devsecfranklin/badge-2018-nolacon/artwork/nola_diecut.bmp

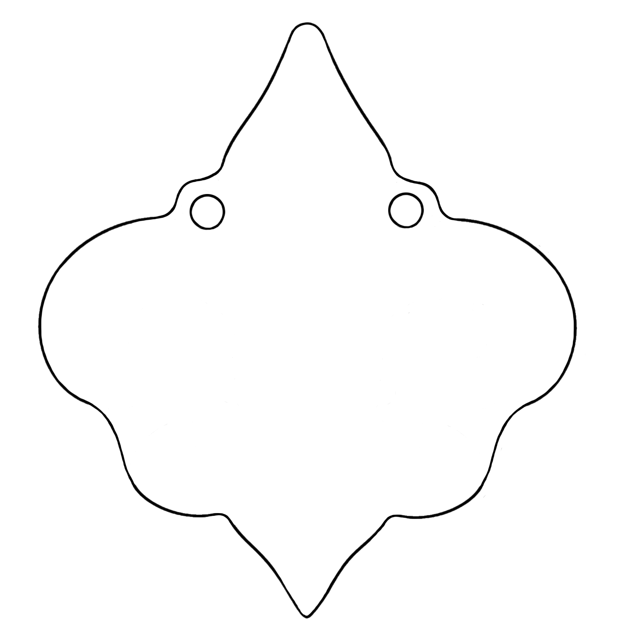
artwork/nola_diecut.bmp
