devsecfranklin/badge-2018-nolacon/artwork/nola_layered_NEW.bmp

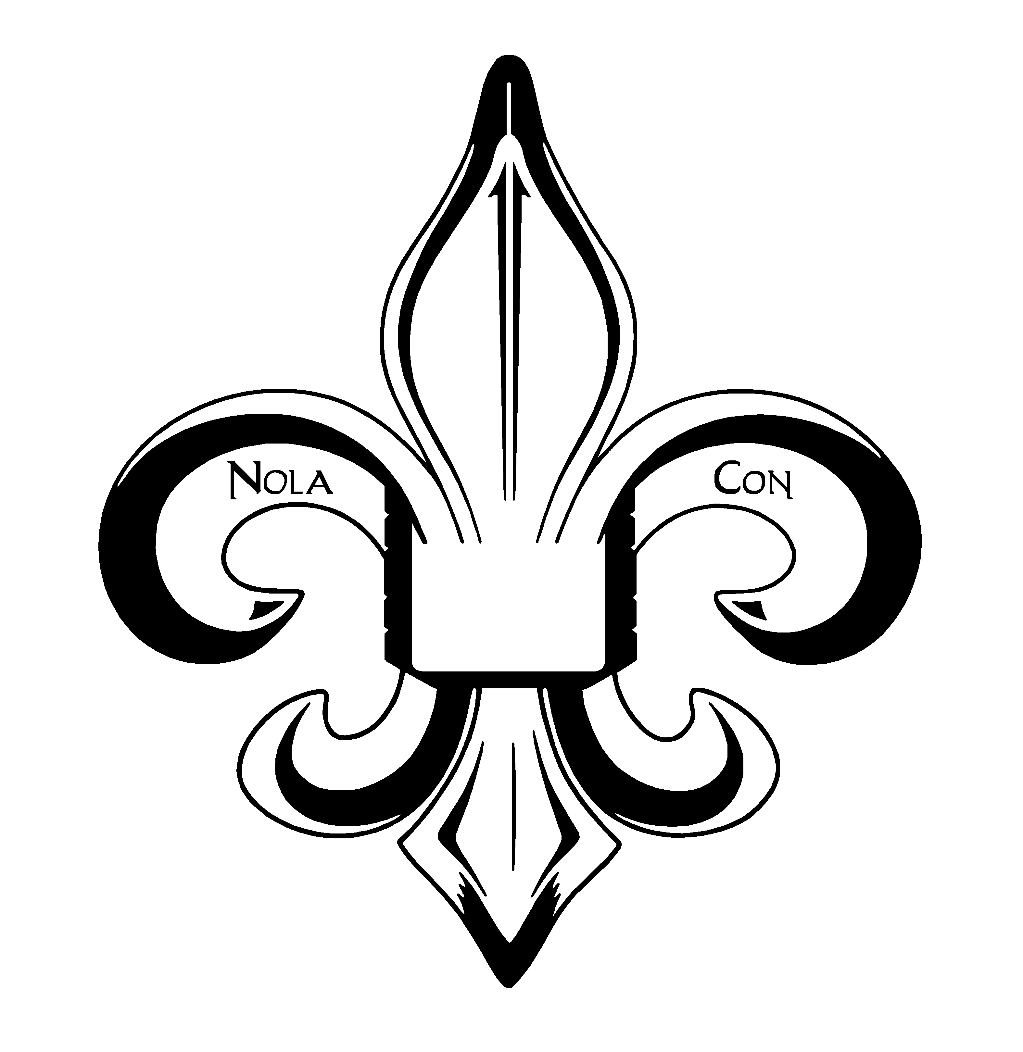
artwork/nola_layered_NEW.bmp
