devsecfranklin/badge-2018-nolacon/images/image1.png

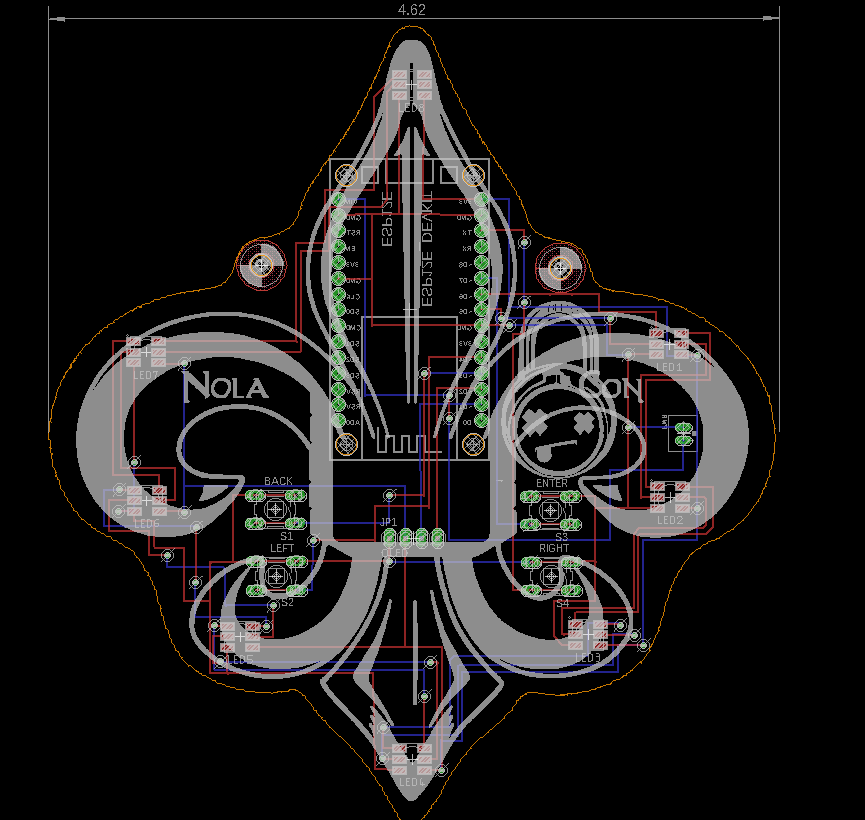
images/image1.png
