devsecfranklin/badge-2018-nolacon/images/image2.jpeg

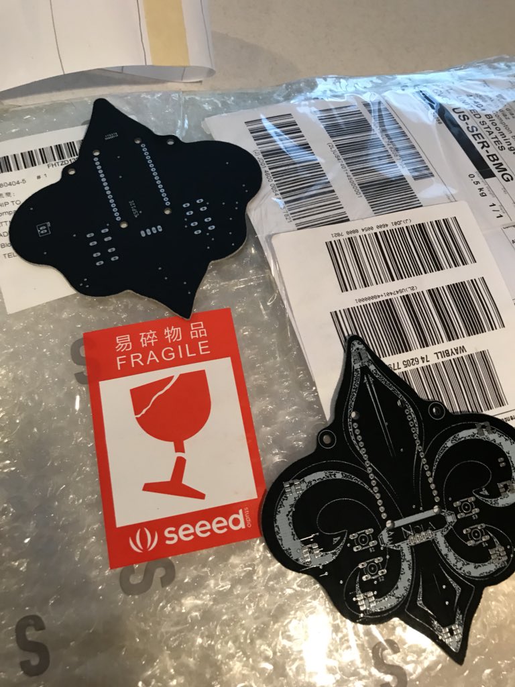
images/image2.jpeg
