devsecfranklin/badge-2018-nolacon/images/image3.jpg

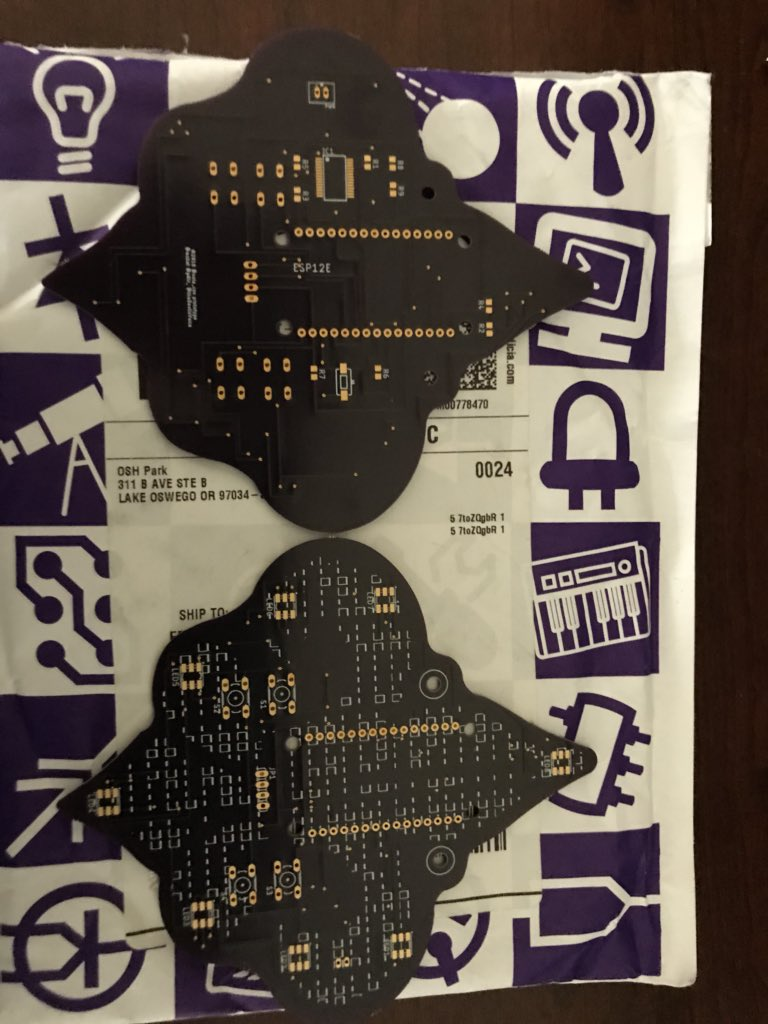
images/image3.jpg
