devsecfranklin/badge-2018-nolacon/images/image4.jpg

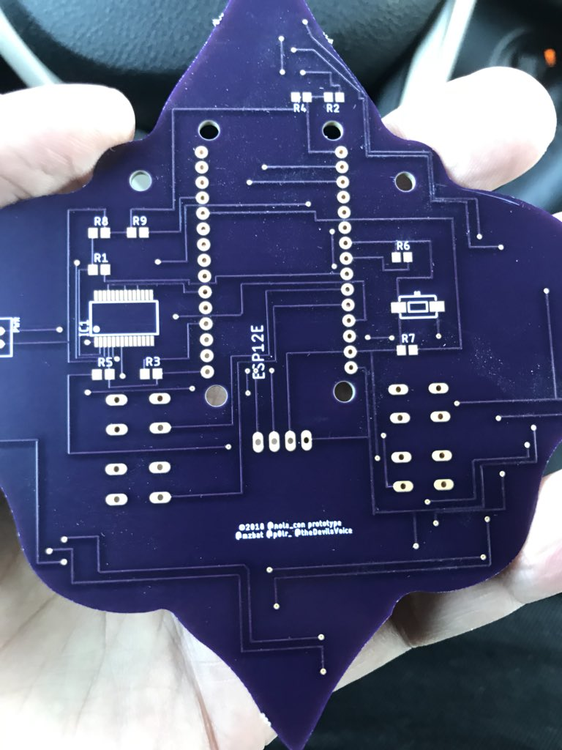
images/image4.jpg
