devsecfranklin/badge-2018-nolacon/images/image6.jpg

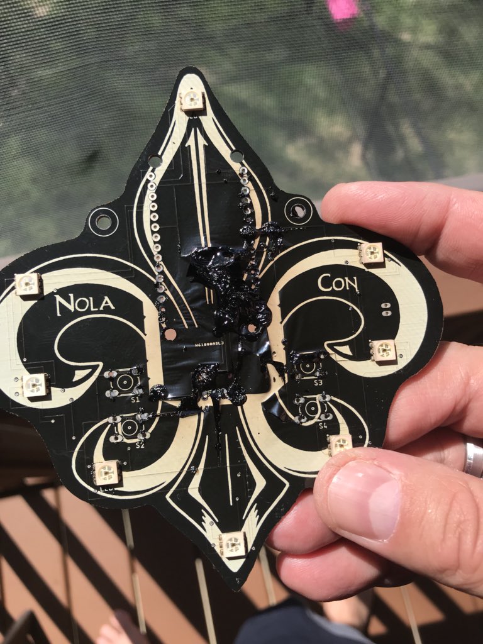
images/image6.jpg
