devsecfranklin/badge-2018-nolacon/images/image7.jpg

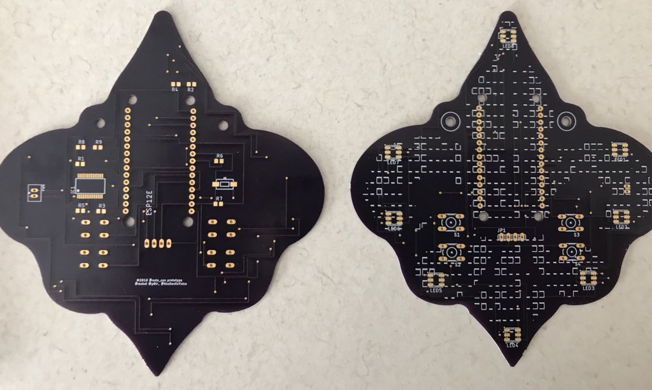
images/image7.jpg
