devsecfranklin/badge-2018-nolacon/images/image8.jpeg

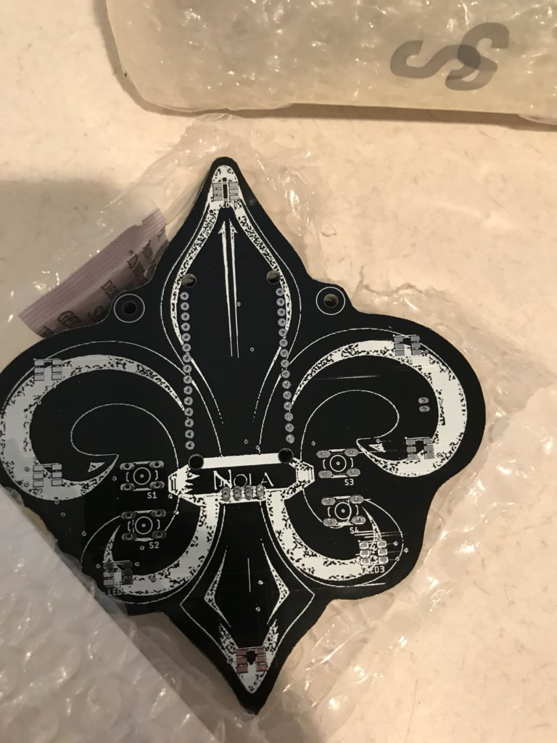
images/image8.jpeg
