devsecfranklin/badge-2018-nolacon/src/nola2/nola.h

/*
 *  ____  _____      _    ____    _  ___     ____ ____  
 * |  _ \| ____|_   / \  |  _ \ _/ |/ _ \ _ / ___| ___| 
 * | | | |  _| (_) / _ \ | | | (_) | | | (_) |   |___ \ 
 * | |_| | |___ _ / ___ \| |_| |_| | |_| |_| |___ ___) |
 * |____/|_____(_)_/   \_\____/(_)_|\___/(_)\____|____/ 
 *                                                    
 *                                                    
 * Author : @theDevilsVoice
 * Date   : March 31, 2018
 * Version: 0.4
 */
 
#ifndef NOLA_H
#define NOLA_H

#define VERSION "0.2"

//SSD1306 display(0x3c, D2, D1);
#define OLED_RESET 2
Adafruit_SSD1306 display(OLED_RESET);

#if (SSD1306_LCDHEIGHT != 64)
#error("Height incorrect, please fix Adafruit_SSD1306.h!");
#endif

// Define which pins to use.
const uint8_t dataPin = D5;
const uint8_t clockPin = D6;

// Set the number of LEDs to control.
const uint16_t ledCount = 8;

// Set the brightness to use (the maximum is 31).
const uint8_t brightness = 1;
const uint16_t minPower = 1;
const uint16_t maxPower = 255 * 31;
const float multiplier = pow(maxPower / minPower, 1.0 / (ledCount - 1));

#define LOGO16_GLCD_HEIGHT 16 
#define LOGO16_GLCD_WIDTH  16 
// character dimensions (for aligning text)
#define CH_WID 6
#define CH_HEI 8
// display dimensions (for aligning text)
#define DP_WID 128
#define DP_HEI 64
#define DP_WID_MID 64
#define DP_HEI_MID 32

int switchPin1 = D3;              
int switchPin2 = D4;
int switchPin3 = D7;
int switchPin4 = D10;

/* 
 * menu 
 * 
 * 1. bling
 *   1.1 cybercop
 *   1.2 rainbow
 *   1.3 chase
 * 2. games
 *    2.1 snake
 *    2.2 pong
 * 3. network   
 *   3.1 wifi scanner
 */


// nola logo
const unsigned char PROGMEM fdl_bmp1 [] = {
  0x0f, 0xff, 0xff, 0xff, 0xff, 0xff, 0xff, 0xff, 0xff, 0xff, 0xff, 0xff, 0xff, 0xff, 0xff, 0xf0, 
  0x0f, 0xff, 0xff, 0xff, 0xff, 0xff, 0xff, 0xff, 0xff, 0xff, 0xff, 0xff, 0xff, 0xff, 0xff, 0xf0, 
  0x0f, 0xff, 0xff, 0xff, 0xff, 0xff, 0xff, 0xff, 0x7f, 0xff, 0xff, 0xff, 0xff, 0xff, 0xff, 0xf0, 
  0x0f, 0xff, 0xff, 0xff, 0xff, 0xff, 0xff, 0xff, 0x7f, 0xff, 0xff, 0xff, 0xff, 0xff, 0xff, 0xf0, 
  0x0f, 0xff, 0xff, 0xff, 0xff, 0xff, 0xff, 0xfe, 0x7f, 0xff, 0xff, 0xff, 0xff, 0xff, 0xff, 0xf0, 
  0x0f, 0xff, 0xff, 0xff, 0xff, 0xff, 0xff, 0xfc, 0xbf, 0xff, 0xff, 0xff, 0xff, 0xff, 0xff, 0xf0, 
  0x0f, 0xff, 0xff, 0xff, 0xff, 0xff, 0xff, 0xf8, 0x1f, 0xff, 0xff, 0xff, 0xff, 0xff, 0xff, 0xf0, 
  0x0f, 0xff, 0xff, 0xff, 0xff, 0xff, 0xff, 0xf4, 0x1f, 0xff, 0xff, 0xff, 0xff, 0xff, 0xff, 0xf0, 
  0x0f, 0xff, 0xff, 0xff, 0xff, 0xff, 0xff, 0xfd, 0x4f, 0xff, 0xff, 0xff, 0xff, 0xff, 0xff, 0xf0, 
  0x0f, 0xff, 0xff, 0xff, 0xff, 0xff, 0xff, 0xe0, 0x27, 0xff, 0xff, 0xff, 0xff, 0xff, 0xff, 0xf0, 
  0x0f, 0xff, 0xff, 0xff, 0xff, 0xff, 0xff, 0xe8, 0x07, 0xff, 0xff, 0xff, 0xff, 0xff, 0xff, 0xf0, 
  0x0f, 0xff, 0xff, 0xff, 0xff, 0xff, 0xff, 0xc0, 0x53, 0xff, 0xff, 0xff, 0xff, 0xff, 0xff, 0xf0, 
  0x0f, 0xff, 0xff, 0xff, 0xff, 0xff, 0xff, 0x80, 0x03, 0xff, 0xff, 0xff, 0xff, 0xff, 0xff, 0xf0, 
  0x0f, 0xf8, 0xfc, 0xff, 0xff, 0xff, 0xff, 0xa5, 0xc1, 0xff, 0xfe, 0x0f, 0xff, 0xff, 0xff, 0xf0, 
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
  0x00, 0x00, 0x00, 0x00, 0x80, 0x00, 0x00, 0x00, 0x00, 0x00, 0x00, 0x01, 0x00, 0x00, 0x00, 0x00, 
  0x00, 0x00, 0x00, 0x00, 0x80, 0x00, 0x00, 0x00, 0x00, 0x00, 0x00, 0x01, 0x00, 0x00, 0x00, 0x00, 
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
};

#endif // NOLA_H


/*


      `..                             .-:/+ooossooooooosssso+/:+hMMMMMMMMMMMMMMMMh+////mMMMMMMMMMMMs/
  `...`                        .:+sss+/-.`                `.:/oshhdmmmMMMMMMMMMMMNds///mMMMMMMMMMMMs
``...                      -+ss+:.                                .:+symMMMMMMMMMMMMMh+/ohNMMMMMMMMM
....                   ./ss/.                                          ./ymNMMMMMMMMMMMho/+hMMMMMMMM
..`                 `/so:`                                                 -omMMMMMMMMMMMms/oNMMMMMM
.`                :ss:                                                        -smNMMMMMMMMMh/oNMMMMM
`               /y+`                                                            `/dNMMMMMMm+//+MMMMM
              /y/                                                                  :hy++o+/////sNMMM
            -y/                                                                      /hs////////yMMM
          `so`                                                                        `od+///////dMM
         -y:                                                                            -ds//////hMM
        +y.   `/`          :y:                                                           `yh//////dM
       os`  `+ddd+.      :dNMMd:                                                           sh/////yM
      ss   /hdddddds-  -hNNNNMMMd/                                         `o:       .ss.   oh////yM
     +y  :hdddddddddmysmNNNNNMMMMMm/`                                    `oNMMd/   `sMMMMy.  sy--:oM
    -h`.hmmmdddddddmmmmmNNNNNMMMMMMMy`                                  /NMMMMMMm+oNMMMMMMMh-`h+..` 
   `h:  :hmmmmddddmmmmmNNNNNNMMMMMd:                                  -dMMMMMMMMMMMMMMMMMMMMMo-d/:/s
   +y     :ymmmmmmmmmmNNNNNNMMMMd:                                     /dMMMMMMMMMMMMMNNNNNh:  oh/oN
  `h:       -ymmmmmmNNNNNNNMMMMs                                         :hMMMMMMMNNNNNNNd:    .mosN
  -h        /mNNNNNNNNNNNNMMMMMMd:                                        :mMMMMNNNNNNNmmh:     yy: 
  os      /mNNNNNNNNNNNMMMMMMMMMMMm/                                    :dMMMMMNNNNNmmmmmmmh/`  +m+ 
  s+    /mMMMMMNNMMMMMMMMMMMMMMMMMMm:                                 `hMMMMMMNNNNNmmmmdddddy-  :m+ 
  y/    /dMMMMMMMMMMMMNMMMMMMMMMMNo                                    .yNMMMMNNNmohmmddddy-    -m+ 
  y+      :hMMMMMMMMMy..sNMMMMMMs`                                       `oNMMNNs.  :yddh/      -m- 
  so        -hMMMMMh.    `sNMMh.                                           `oms.      ./`       /d  
  /h          -yMh-        `+:                                                                  ss  
s+:d.           `                                                                              `dd  
MMMyo                                                                                          +md  
MMMyd.                                                                                        `dd.  
MMMMdy                                                       `.-:/+osyhds.                    sm.   
MMMMNh+                                         `.-:/+osydmNmdhyso+/:++os:                   +N:    
MMMMMdd/                            `-:/+osyhdmmmdhys+/:-.`                                 -m/     
MMMMMMmd/                 `.:+oyhdNMMMMMM+:-.`                                             -h+      
MMMMMMMdh+             /dNMMMMMMMMMMMMMMM:                                                :h-       
MMMMMMMMdhs`           /:NMMMMMMMMMMMMMMMo                                               +h.        
MMMMMMMMMMhh:            dMMMMMMMMMMMMMMMh                                             .ys`   .++:  
MMMMMMMMMMMmds`          oMMMMMMMMMMMMMMMm                                           `+d/     -.    
NysmddMMMy+/smmo`        +MMMMMMMMMMMMMMMM                                          /h+`            
.     .y.     :/ho.      `NMMMMMMMMMMMMMMN                                       `/h+               
          :/     :yy:     /NMMMMMMMMMMMMm:                                     -od+`                
 `ydo```/dMMho.   yMmho-   .sdNNNNNNNho-                                    .+hy/`                  
`yMMMMMMMMMMMMMy+oNMMNmdho:`                                            `-ohy/`                     
MMMMMMMMMMMMMMMMMMMMMMMMNhhhyo/.                                    `:ohho:`                        
MMMMMMMMMMMMMMMMMMMMMMMMMMMNdshdhyo/-.                        `-/oyhs+:`                            
MMMMMMMMMMMMMMMMMMMMMMMMMMmm-   ` .:+osyyyo++/:::---:://+ossyyso/-`                                 
++++++++++++++++++++++++:                 `..-:/:///:::--`                                          
 
 
 */
